meunomemauricio/hygrometer/images/final_top.jpg

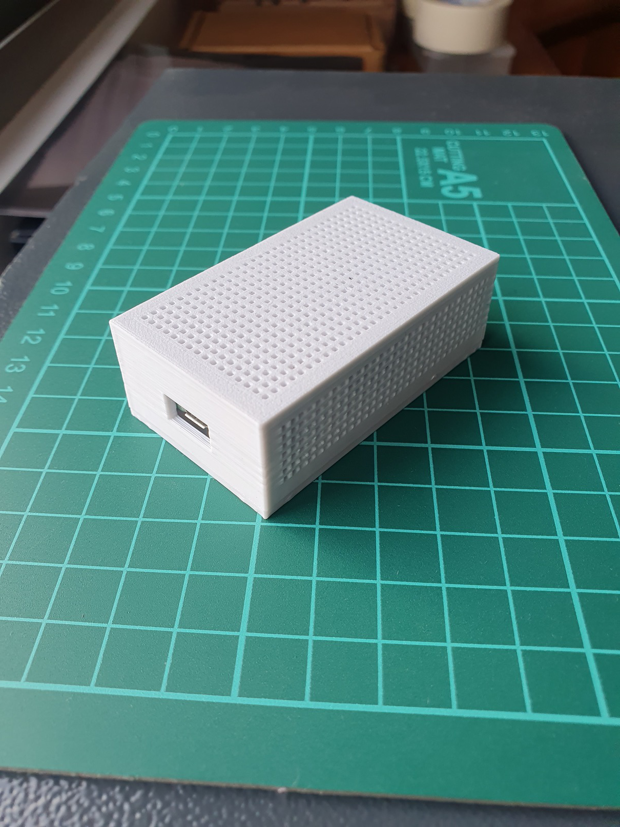
images/final_top.jpg
